Quantum-Electronic-Devices/One-Inch-Photodiode/simulations/sfh203.asc

C1: cap; 11p
C2: cap; 2p
I1: current; SINE(100u 100u 1); AC 1
R1: res; 10k
R2: res; 300
R3: res; 1.2k
U1: ADA4898
U2: ADA4898
V1: voltage; 12
V2: voltage; 12
Named nets: 0, V+, V-
.tran 1
.ac dec 100 10 10Meg
